ishkabbible/Befaco_VCADSR_v1.1/VCADSR built 1.jpg

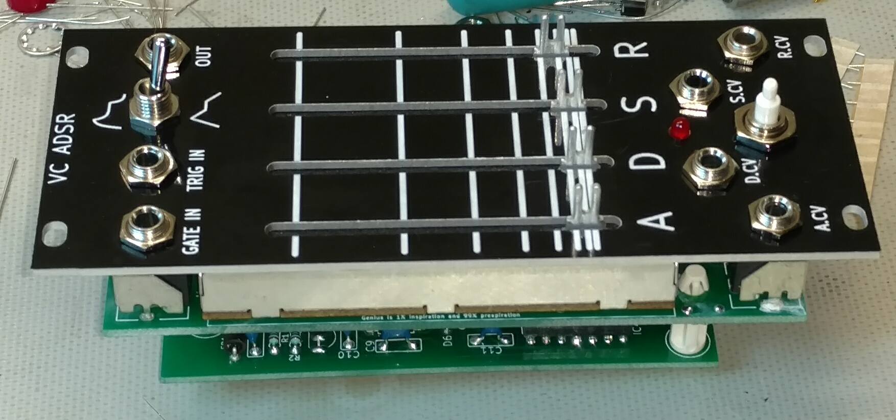
VCADSR built 1.jpg
