ishkabbible/Befaco_VCADSR_v1.1/VCADSR built 5 glamor shot.jpg

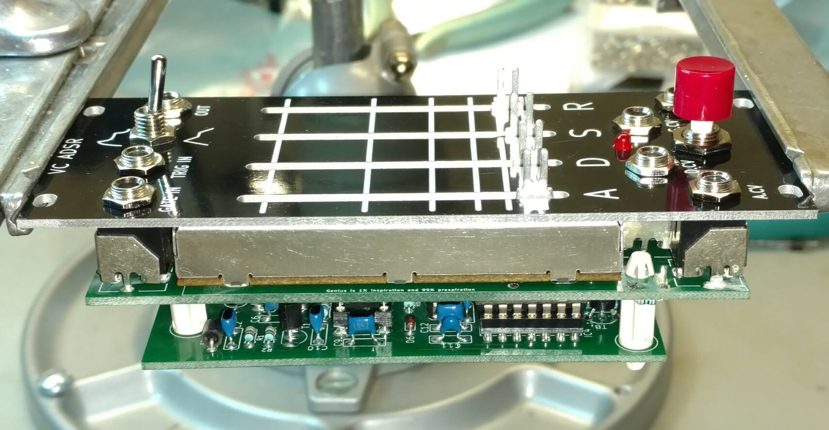
VCADSR built 5 glamor shot.jpg
