ishkabbible/Befaco_VCADSR_v1.1/VCADSR built 6 back.jpg

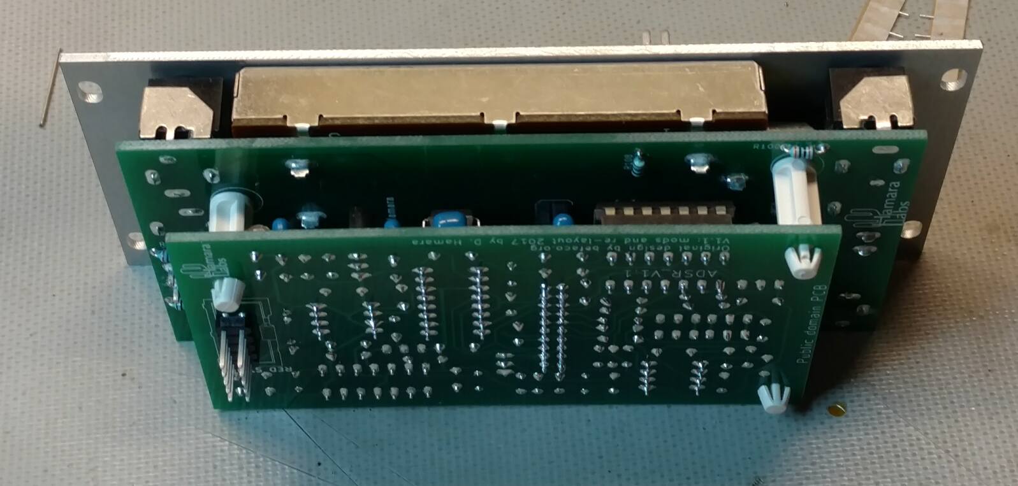
VCADSR built 6 back.jpg
