ishkabbible/Befaco_VCADSR_v1.1/VCADSR built 7 side.jpg

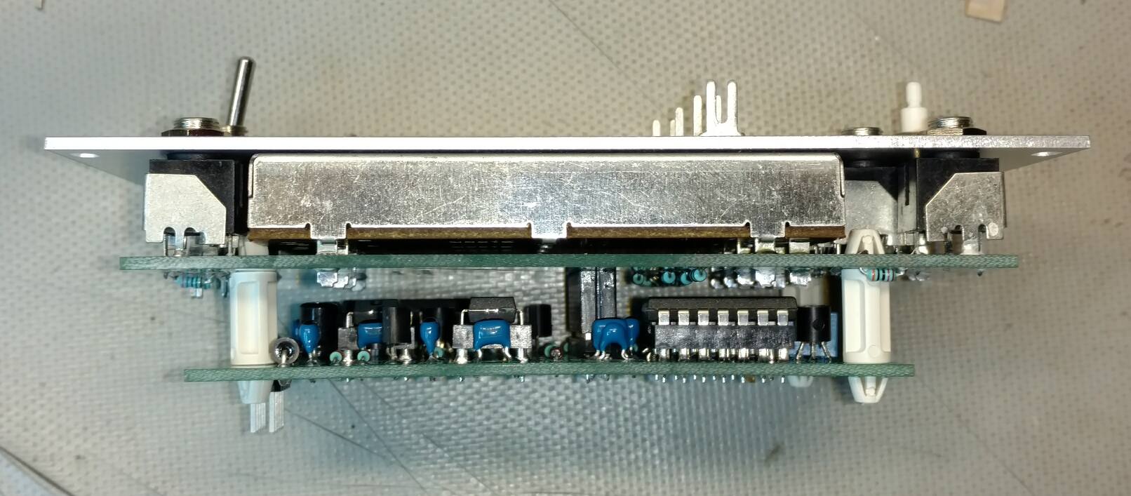
VCADSR built 7 side.jpg
