ishkabbible/Befaco_VCADSR_v1.1/VCADSR built both boards.jpg

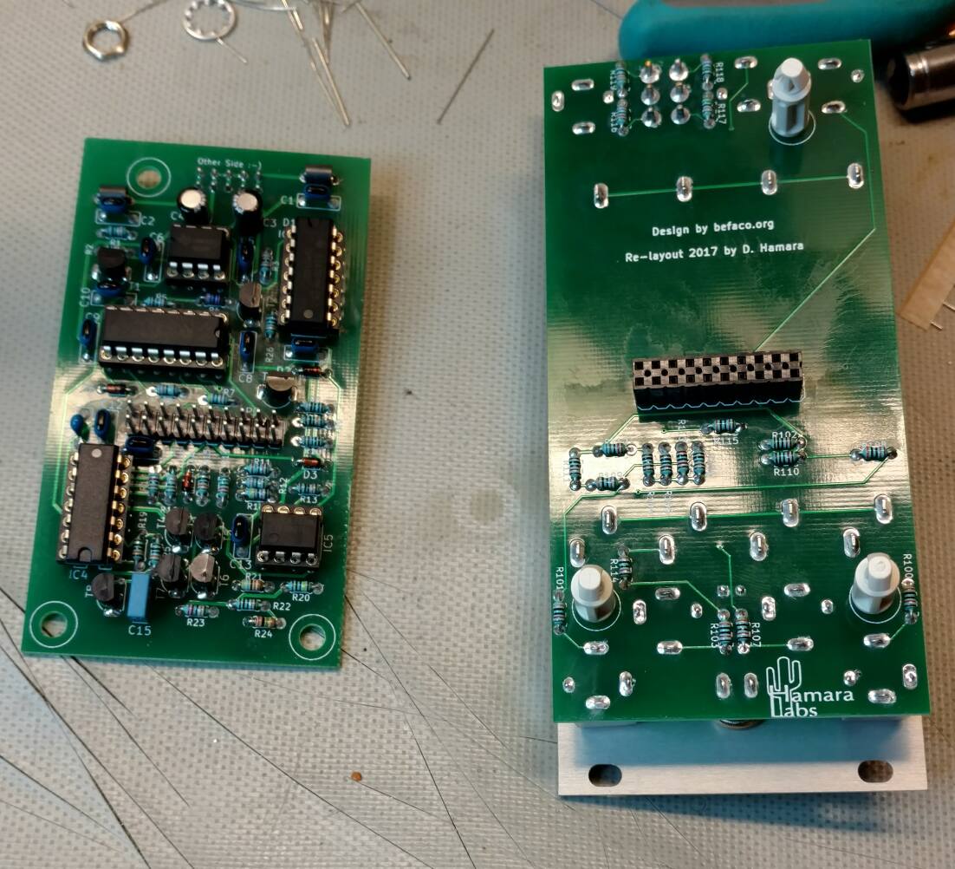
VCADSR built both boards.jpg
