ishkabbible/Befaco_VCADSR_v1.1/full assembly 3D front final 2.jpg

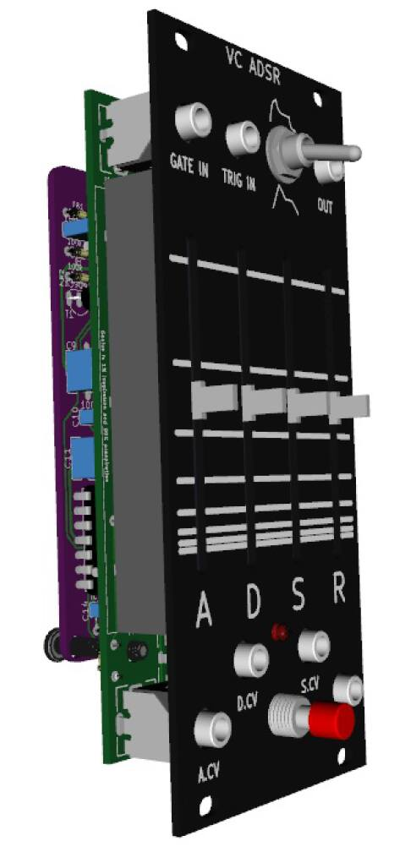
full assembly 3D front final 2.jpg
