ishkabbible/Befaco_VCADSR_v1.1/full assembly 3D perspective final 1.jpg

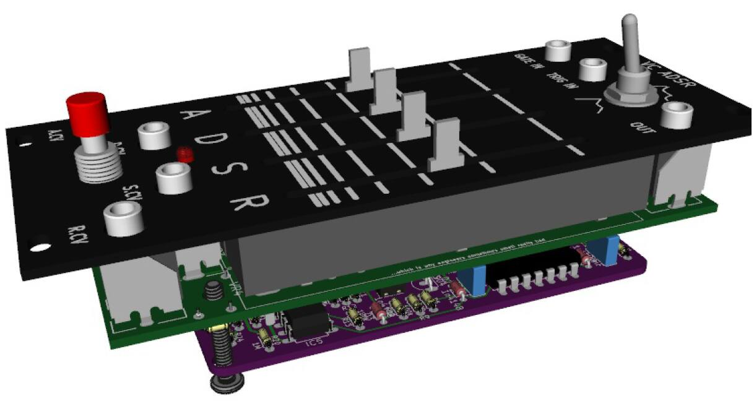
full assembly 3D perspective final 1.jpg
